Juleinn/Marty1910/main/bm64_driver.h

#ifndef BM64_DRIVER_H
#define BM64_DRIVER_H

#define BM64_NOERROR 0
#define BM64_DATA_TOOSHORT 1

int bm64_init();
void bm64_test();

void bm64_accept_call();
void bm64_reject_call();
void bm64_end_call();

void bm64_set_gain(uint8_t HF, uint8_t mic);

void __attribute__((weak)) bm64_on_incomming_call();
void __attribute__((weak)) bm64_on_call_status_idle();

void __attribute__((weak)) bm64_on_outgoing_call();

#define CALL_STATUS_INCOMMING_CALL 0x02
#define CALL_STATUS_OUTGOING_CALL 0x03
#define CALL_STATUS_IDLE 0x00

void bm64_prepare_flash_mode();

#endif
