Juleinn/Marty1910/main/ag1171_driver.h

#ifndef AG1171_H_INCLUDED
#define AG1171_H_INCLUDED 

#include <stdio.h>
#include <stdlib.h>
#include <stdbool.h>

void ag1171_init();
void ag1171_ring_once();
void ag1171_ring_loop();

bool ag1171_is_offhook();

void ag1171_start_ringing();
void ag1171_stop_ringing();

void __attribute__((weak)) ag1171_on_phone_offhook();
void __attribute__((weak)) ag1171_on_phone_onhook();

void ag1171_ring_short();

#endif
